simpkins/mantyl/src/components/sx1509/include/SX1509.h

// Copyright (c) 2022, Adam Simpkins
#pragma once

#include "I2cDevice.h"
#include "Result.h"

#include <endian.h>
#include <utility>

namespace mantyl {

class SX1509 {
public:
  SX1509(I2cMaster &bus, uint8_t addr, gpio_num_t int_pin)
      : dev_{bus, addr}, int_pin_{int_pin} {}
  explicit SX1509(I2cDevice &&device) : dev_{std::move(device)} {}
  ~SX1509();

  uint8_t address() const {
    return dev_.address();
  }

  [[nodiscard]] esp_err_t init();

  /**
   * Configure the row and column pins and enable keypad scanning.
   *
   * This calls prepare_keypad() followed by enable_keypad_engine().
   */
  [[nodiscard]] esp_err_t configure_keypad(uint8_t rows, uint8_t columns);

  /**
   * Prepare the row and column pins directions and pull-ups for keypad
   * scanning.
   */
  [[nodiscard]] esp_err_t prepare_keypad();

  /**
   * Enable the keypad engine.
   *
   * prepare_keypad() should have been called successfully before calling
   * enable_keypad_engine()
   */
  [[nodiscard]] esp_err_t enable_keypad_engine(uint8_t rows, uint8_t columns);

  /**
   * Read the keypad data.
   *
   * The keypad engine must be enabled.
   *
   * Returns a 16 bit integer, where the least significant byte indicates the
   * row that was being scanned, and the most significant byte indicate which
   * columns were active triggering the interrupt.
   *
   * Beware, if read_keypad() is called when the SX1509 is not asserting the
   * interrupt pin, invalid data can be read, where either KeyData1 or
   * KeyData2 is 0 while the other is non-zero.
   *
   * The SX1509 appears to set KeyData1 and KeyData2 sequentially, and then
   * asserts interrupt afterwards.  It clears all 3 when KeyData2 is read.
   * Reading at arbitrary points in time can result in reading only valid data
   * from only 1 register, and a 0 value from the other.  Reading KeyData2 can
   * also reset the state back to 0 in the middle of while it is being updated,
   * resulting in an invalid read on the next attempt as well.
   */
  Result<uint16_t> read_keypad();

  int read_interrupt();

  gpio_num_t interrupt_pin() const {
    return int_pin_;
  }

private:
  // Register addresses
  enum Reg : uint8_t {
    // I/O pull up: 0 disabled, 1 enabled
    // (defaults to disabled for all I/Os)
    PullUpB = 0x06,
    PullUpA = 0x07,
    // I/O pull down: 0 disabled, 1 enabled
    // (defaults to disabled for all I/Os)
    PullDownB = 0x08,
    PullDownA = 0x09,
    // I/O open drain config: 0 is push-pull, 1 is open drain
    // (defaults to push-pull for all I/Os)
    OpenDrainB = 0x0a,
    OpenDrainA = 0x0b,
    // I/O direction: 1 is input, 0 is output
    // (defaults to input for all I/Os)
    DirB = 0x0e,
    DirA = 0x0f,
    IntrMaskA = 0x13,
    Clock = 0x1e,
    Misc = 0x1f,
    DebounceConfig = 0x22,
    DebounceEnableB = 0x23,
    DebounceEnableA = 0x24,
    KeyConfig1 = 0x25,
    KeyConfig2 = 0x26,
    KeyData1 = 0x27,
    KeyData2 = 0x28,
    Reset = 0x7d,
  };

  enum class ClockSource : uint8_t {
    Off = 0x00,
    External = 0x01,
    Internal2MHZ = 0x02,
  };
  enum class OscPinFuncion : uint8_t {
    Input = 0,
    Output = 1,
  };

  SX1509(SX1509 const &) = delete;
  SX1509 &operator=(SX1509 const &) = delete;

  /**
   * source:
   *   Source for fOSC frequency.
   *   - Internal2MHz: Internal 2Mhz clock
   *   - External: Driven from OSC pin.  pin_fn should be set to Input.
   *
   * led_divider (0x0 to 0x7):
   *   Controls frequency of clock for LED driver:
   *   - 0x0: off
   *   - otherwise: ClkX = fOSC / (2^(divider -1))
   *
   *   In other words:
   *   - 1: 2Mhz
   *   - 2: 1Mhz
   *   - 3: 500khz
   *   - 4: 250Khz
   *   - 5: 125Khz
   *   - 6: 62.5Khz
   *   - 7: 31.25Khz
   *
   * pin_fn:
   *   Controls if the OSC pin should be used as input (OSCIN, for use with an
   *   external clock source), or output (OSCOUT, to generate an external
   *   signal from the external clock).
   *
   * oscout_freq (0x0 to 0xf):
   *   Controls frequency of OSCOUT pin, if it is configured as an output.
   *   - 0x0: 0Hz, permanent 0 logic level
   *   - 0xf: 0Hz, permanent 1 logic level
   *   - otherwise: fOSCOUT = fOSC / (2^(oscout_freq-1))
   */
  [[nodiscard]] esp_err_t
  configure_clock(ClockSource source,
                  uint8_t led_divider = 1,
                  OscPinFuncion pin_fn = OscPinFuncion::Input,
                  uint8_t oscout_freq = 0);

  [[nodiscard]] esp_err_t
  write_data(uint8_t addr, const void *data, size_t size);
  [[nodiscard]] esp_err_t write_u8(uint8_t addr, uint8_t value) {
    return write_data(addr, &value, sizeof(value));
  }
  [[nodiscard]] esp_err_t write_u16be(uint8_t addr, uint16_t value) {
    const uint16_t be = htobe16(value);
    return write_data(addr, &be, sizeof(be));
  }

  esp_err_t read_data(uint8_t addr, void *data, size_t size);
  template<typename IntType>
  Result<IntType, esp_err_t> read_int(uint8_t addr) {
    IntType value;
    auto rc = read_data(addr, &value, sizeof(value));
    if (rc == ESP_OK) {
      return make_result(value);
    }
    return make_error<IntType>(rc);
  }
  Result<uint8_t, esp_err_t> read_u8(uint8_t addr) {
    return read_int<uint8_t>(addr);
  }
  Result<uint16_t, esp_err_t> read_u16be(uint8_t addr) {
    return read_int<uint16_t>(addr).and_then(
        [](uint16_t x) { return be16toh(x); });
  }

  I2cDevice dev_;
  gpio_num_t int_pin_{GPIO_NUM_NC};
  gpio_num_t reset_pin_{GPIO_NUM_NC};
  bool initialized_{false};
  bool keypad_configured_{false};
};

} // namespace mantyl
