simpkins/mantyl/src/v1/main/Keyboard.h

// Copyright (c) 2022, Adam Simpkins
#pragma once

#include "keyboard/Keypad.h"

#include <array>
#include <cstdint>

namespace mantyl {

class KeymapDB;

class Keyboard {
public:
  Keyboard(I2cMaster &i2c_left,
           I2cMaster &i2c_right,
           const KeymapDB &keymap_db);

  /**
   * Initialize the keypads.
   *
   * This method is called from the main task, before the keyboard task has
   * started.
   */
  [[nodiscard]] esp_err_t early_init();

  /**
   * Perform additional initialization from the keyboard task, when it first
   * starts.
   */
  [[nodiscard]] esp_err_t kbd_task_init();

  bool should_boot_in_debug_mode();

  std::chrono::milliseconds tick(std::chrono::steady_clock::time_point now);

  void generate_report(std::array<uint8_t, 6> &keycodes, uint8_t &modifiers);

private:
  Keyboard(Keyboard const &) = delete;
  Keyboard &operator=(Keyboard const &) = delete;

  void send_hid_report();

  void on_key_press(bool is_left, uint8_t row, uint8_t col);
  void on_key_release(bool is_left, uint8_t row, uint8_t col);
  void on_key_change(bool is_left, uint8_t row, uint8_t col, bool press);

  const KeymapDB* keymap_db_{nullptr};
  Keypad left_;
  Keypad right_;
  bool need_to_send_report_{false};
};

} // namespace mantyl
