simpkins/mantyl/src/App.cpp

// Copyright (c) 2022, Adam Simpkins
#include "App.h"

#include "esp_util.h"

namespace mtl {

App::App()
    : display_{Display::adafruit128x32(&Wire, kScreenAddress)},
      leftIO_{&Wire, kSX1509AddressLeft} {}

void App::setup() {
  Serial.begin(kSerialBaudRate);

  Serial.println("mantyl init");
  if (!display_.begin()) {
    Serial.println("display initialization failed");
    set_sleep_timer_wakeup(std::chrono::seconds{10});
    esp_deep_sleep_start();
  } else {
    Serial.println("display initialization success!");
  }

  display_.clearDisplayBuffer();
  display_.canvas().setTextSize(1);      // Normal 1:1 pixel scale
  display_.canvas().setTextColor(1);     // Draw white text
  display_.canvas().setCursor(0, 0);     // Start at top-left corner
  display_.canvas().cp437(true);         // Use full 256 char 'Code Page 437' font
  flushDisplay();
  writeMsg("init");
  flushDisplay();

  if (!leftIO_.begin()) {
    // writeMsg("io init failed");
    Serial.println("io init failed");
  } else {
    // writeMsg("io init success");
    Serial.println("io init success");
    leftIO_.configure_keypad(kLeftRows, kLeftCols);
  }

  pinMode(21, INPUT_PULLUP);
}

void App::loop() {
  ++counter_;
  display_.clearDisplayBuffer();
  display_.canvas().setCursor(0, 0);
  display_.canvas().print("loop: ");
  display_.canvas().print(counter_);

  display_.canvas().setCursor(0, 16);
  display_.canvas().print("int: ");
  const auto gpio = digitalRead(21);
  display_.canvas().print(gpio, HEX);

  display_.canvas().setCursor(0, 8);
  display_.canvas().print("keys: ");
  const auto key_data = leftIO_.read_keypad();
  display_.canvas().print(key_data, HEX);

  flushDisplay();
  delay(50);
}

void App::writeMsg(std::string_view msg) {
  for (char c : msg) {
    display_.canvas().write(c);
  }
  flushDisplay();
}

void App::flushDisplay() {
  if (!display_.flush()) {
    Serial.println("display flush failed");
  }
}

} // namespace mtl
